marcobrianza/wemakecolors/design/production/wmc_9_diffuser.dxf

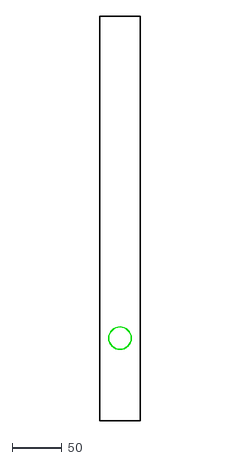
[picture p16: CAD file, 2016-03-03]
design/production/wmc_9_diffuser.dxf
40.3 x 407.0
