marcobrianza/wemakecolors/design/production/8-bottom.dxf

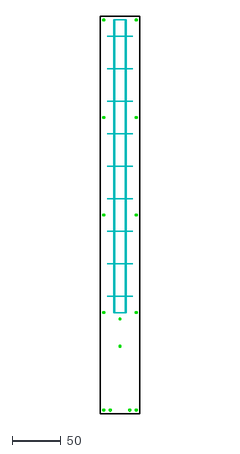
[picture p17: CAD file, 2016-03-03]
design/production/8-bottom.dxf
40.3 x 407.0
